tomaskovacik/fordacp/hw/DSC_1272.JPG

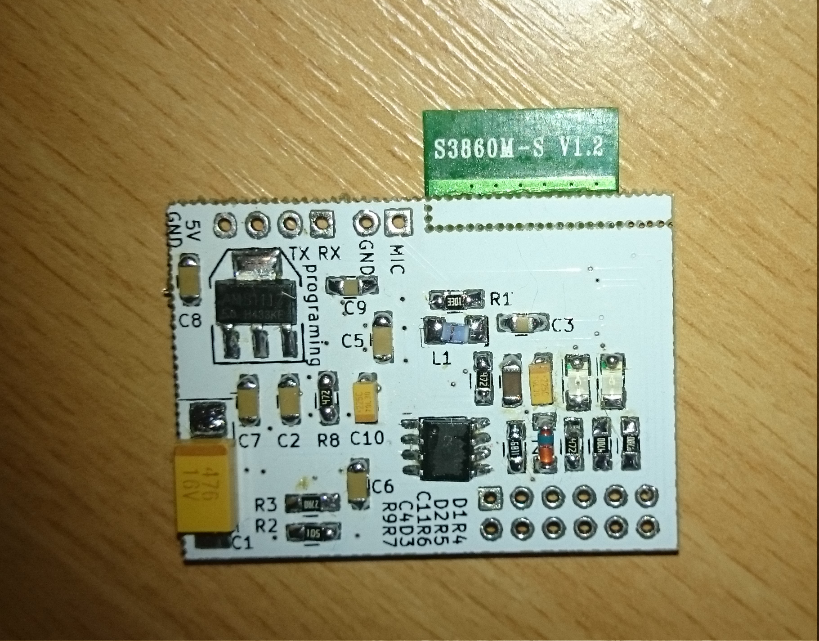
hw/DSC_1272.JPG
