tomaskovacik/fordacp/hw/DSC_1274.JPG

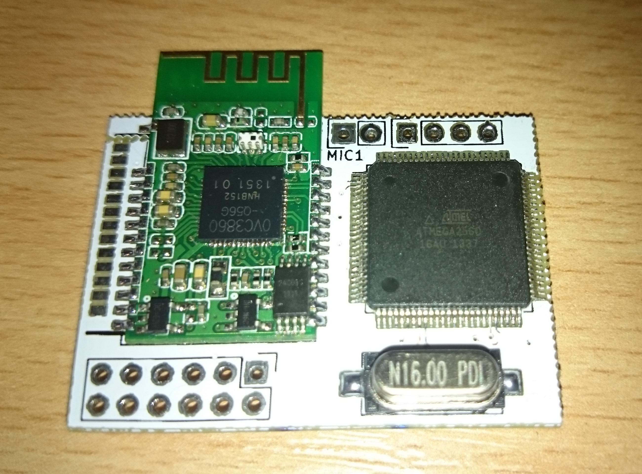
hw/DSC_1274.JPG
